lucasshawn/modelx_frunk/docs/images/frunk_calibrated_profile.png

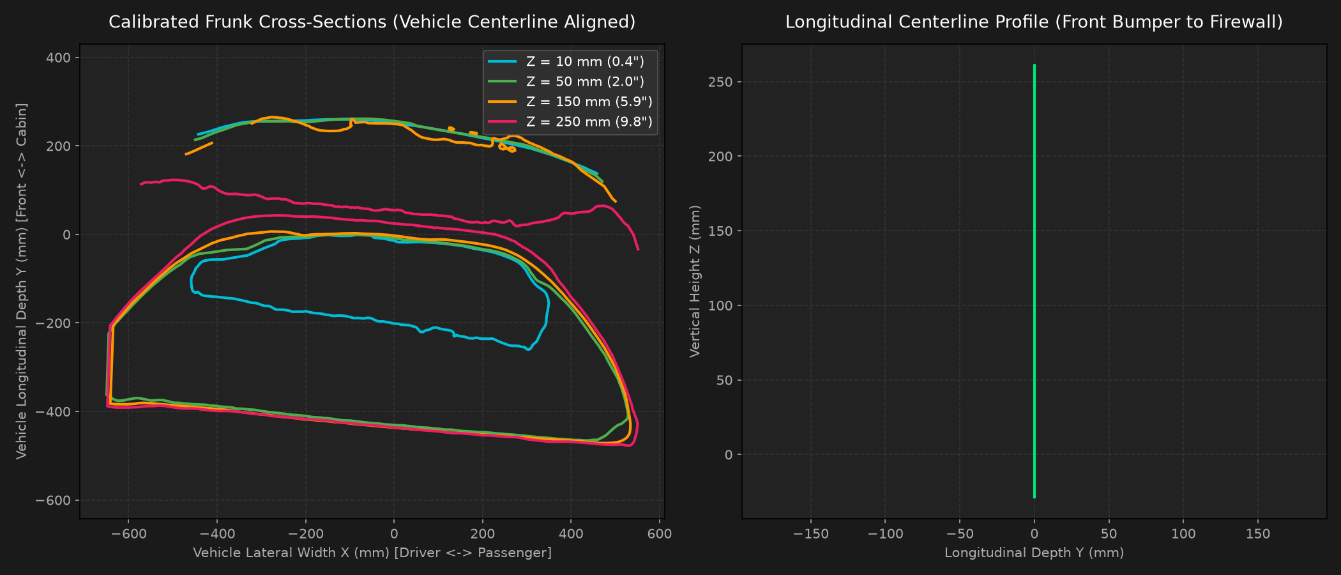
docs/images/frunk_calibrated_profile.png
